SmallCoral/STM32-Sensor-Display/pcb/ssd/review/mcu_footprint_dimensioned.pdf

# STM32C562CET6 专用封装尺寸与脚号核对 / A2

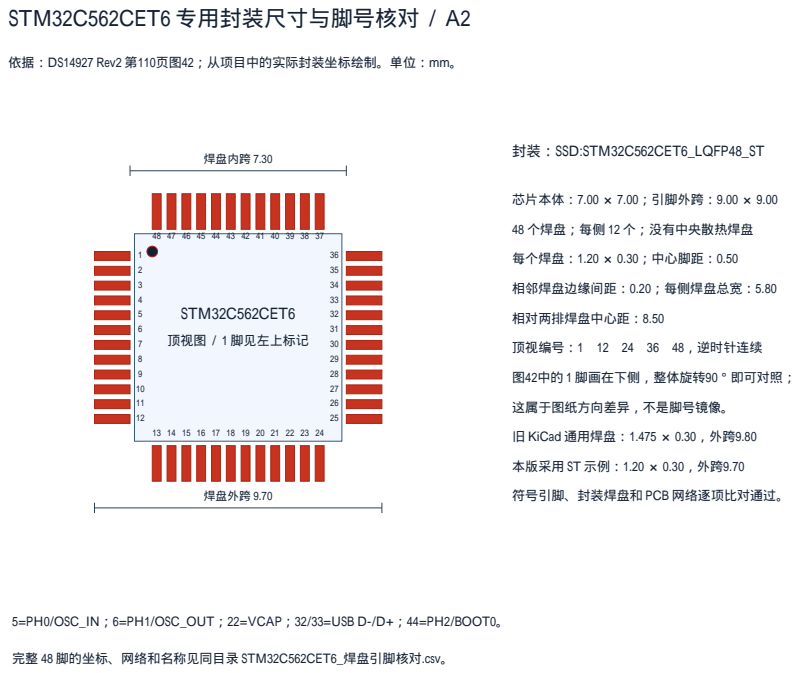
[picture p14: page 1]
STM32C562CET6; 顶视图 / 1 脚见左上标记; 焊盘外跨 9.70; 焊盘内跨 7.30; 封装：SSD:STM32C562CET6_LQFP48_ST; 芯片本体：7.00 × 7.00；引脚外跨：9.00 × 9.00; 每个焊盘：1.20 × 0.30；中心脚距：0.50; 相邻焊盘边缘间距：0.20；每侧焊盘总宽：5.80; 相对两排焊盘中心距：8.50; 顶视编号：1→12→24→36→48，逆时针连续; 图42中的 1 脚画在下侧，整体旋转90°即可对照；; 这属于图纸方向差异，不是脚号镜像。; 旧 KiCad 通用焊盘：1.475 × 0.30，外跨9.80; 5=PH0/OSC_IN；6=PH1/OSC_OUT；22=VCAP；32/33=USB D-/D+；44=PH2/BOOT0。

依据：DS14927 Rev2 第110页图42；从项目中的实际封装坐标绘制。单位：mm。

48 个焊盘；每侧 12 个；没有中央散热焊盘

本版采用 ST 示例：1.20 × 0.30，外跨9.70

符号引脚、封装焊盘和 PCB 网络逐项比对通过。

完整 48 脚的坐标、网络和名称见同目录 STM32C562CET6_焊盘引脚核对.csv。

# MCU 封装 1:1 对位图

### 按实际大小 / 100% 打印；关闭适合页面。先测量下方 20mm 标尺。

本体7×7mm；焊盘外跨9.70mm；1脚标记位于左上。

20mm 标尺
